kbirchard/mcphail-update/research/2015-Insect-Biometrics-Optoacoustic-Signal-McPhail-s023.TIF

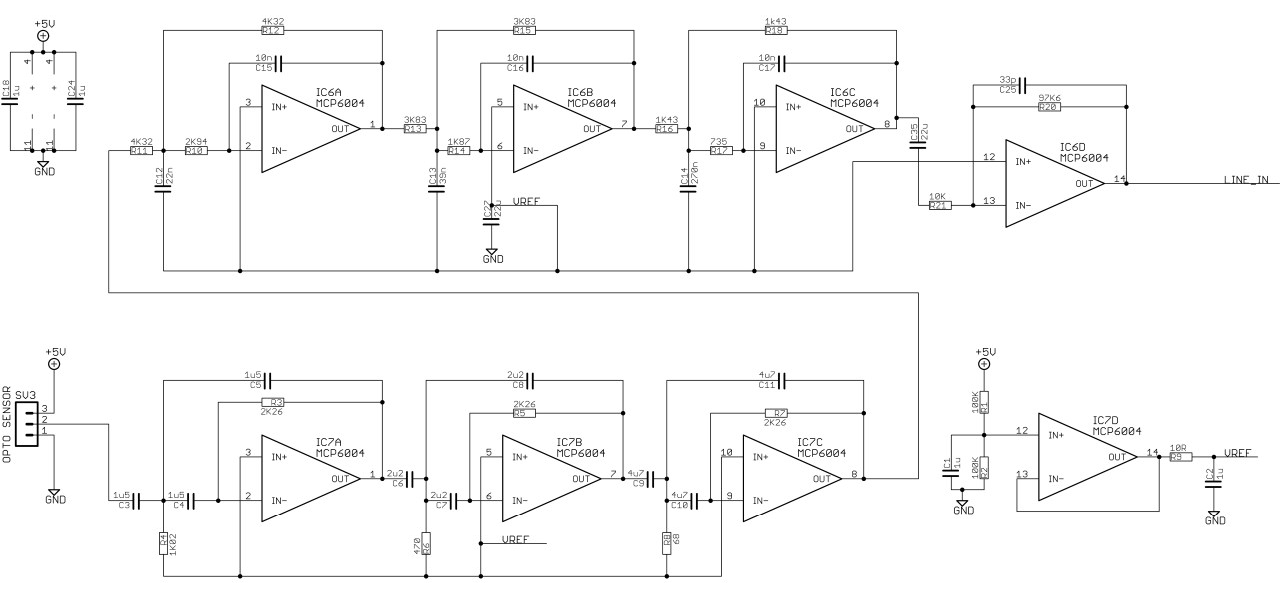
research/2015-Insect-Biometrics-Optoacoustic-Signal-McPhail-s023.TIF
