kbirchard/mcphail-update/research/2015-Insect-Biometrics-Optoacoustic-Signal-McPhail-s026.TIF

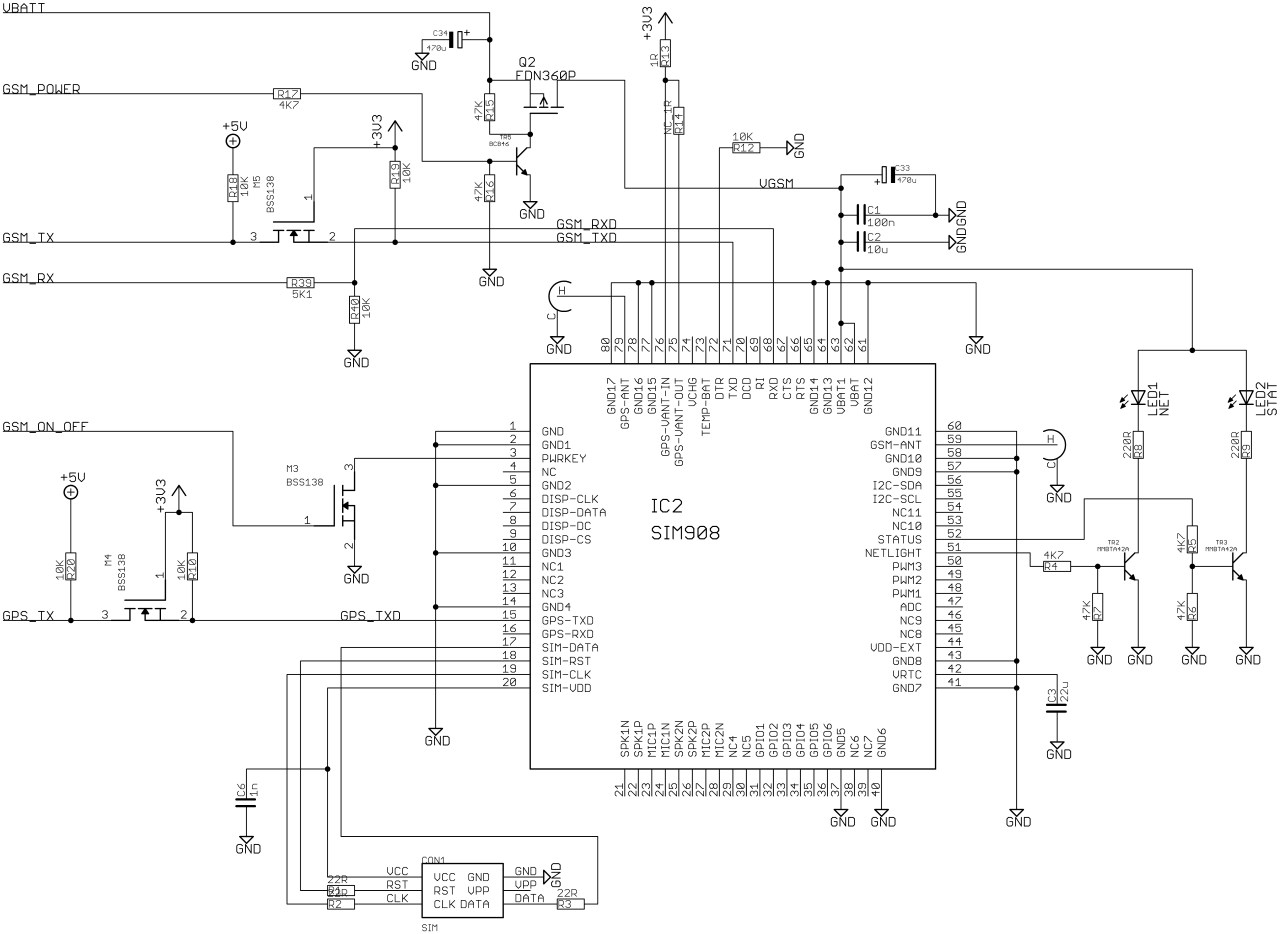
research/2015-Insect-Biometrics-Optoacoustic-Signal-McPhail-s026.TIF
