kbirchard/mcphail-update/research/2015-Insect-Biometrics-Optoacoustic-Signal-McPhail-s027.TIF

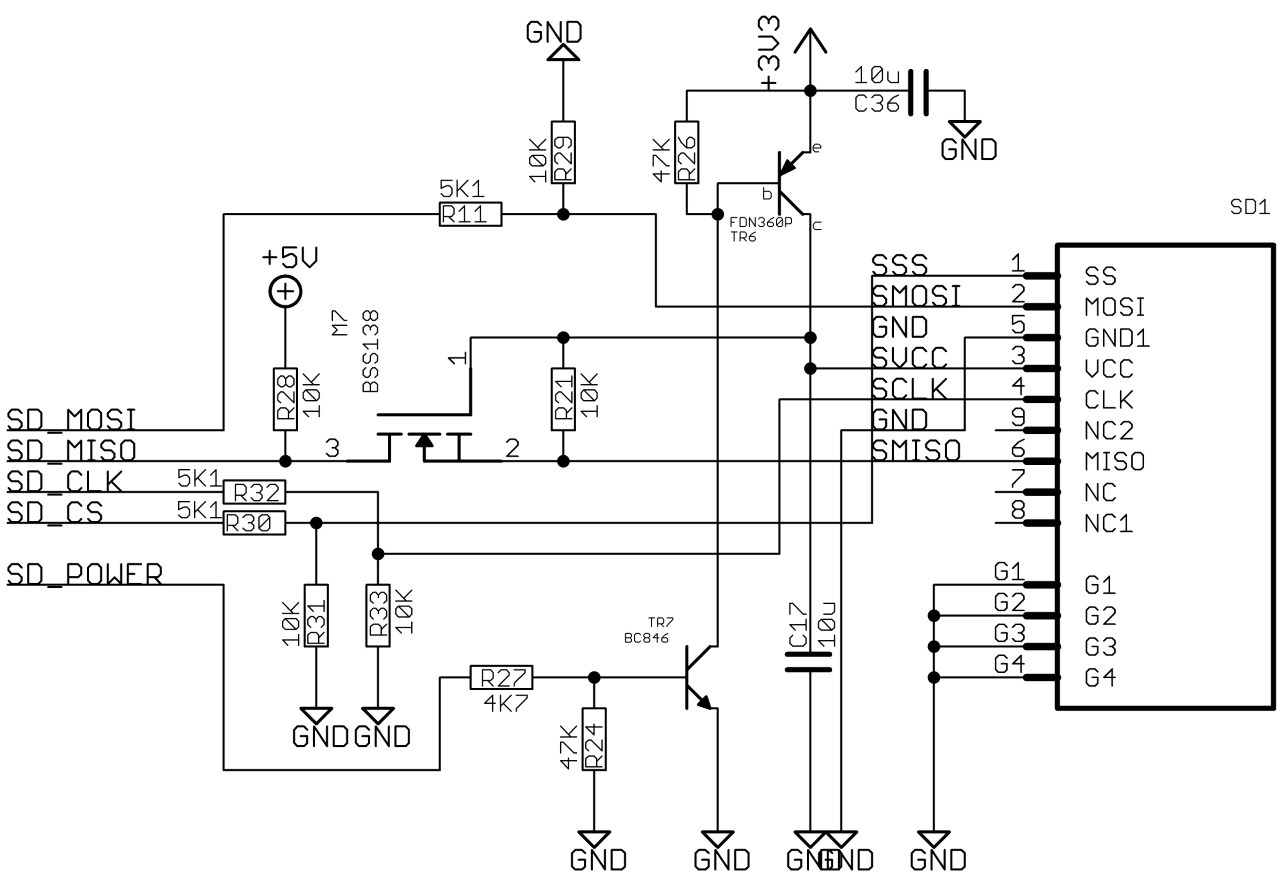
research/2015-Insect-Biometrics-Optoacoustic-Signal-McPhail-s027.TIF
