kbirchard/mcphail-update/research/signalconditioning-rearranged.png

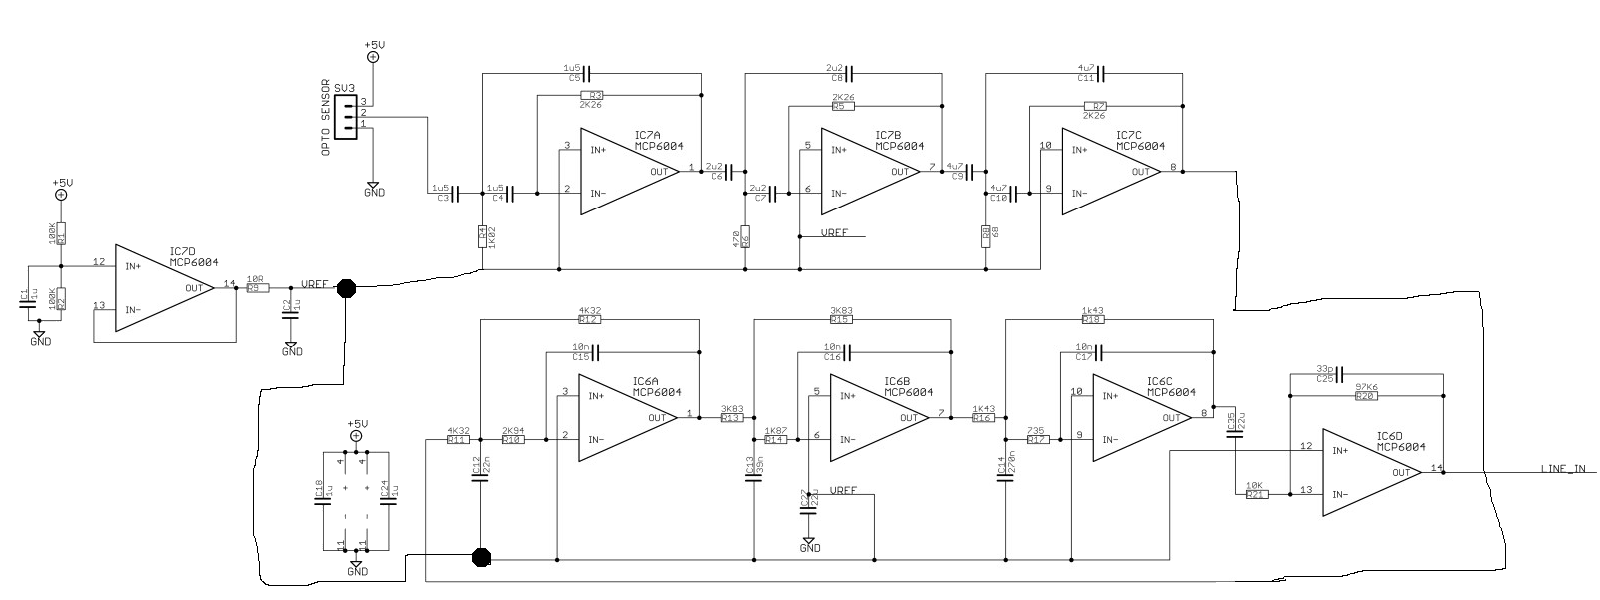
research/signalconditioning-rearranged.png
