kbirchard/mcphail-update/hardware/mcphail-ir-emitter-board/bom/mcphail-ir-emitter-board-v1.0-bom-mouser.csv

Ref | Qty | Qty3 | Description | Mouser PN
LED1 LED10 LED2 LED3 LED4 LED5 LED6 LED7 LED8 LED9 | 10 | 30 | LED IR 850NM TH SFH4356 | 720-SFH4356
