kbirchard/mcphail-update/hardware/mcphail-main-board/bom/mcphail-main-board-v1.0-bom-adafruit.csv

Ref | Qty | Qty3 | Description | Adafruit PN
B1 | 1 | 3 | Lithium Ion Polymer Battery - 3.7v 500mAh | 1578
J7 | 1 | 3 | ADAFRUIT FONA 808 + GPS | 2542
