kbirchard/mcphail-update/hardware/mcphail-ir-emitter-board/bom/mcphail-ir-emitter-board-v1.0-bom-seeed.csv

Location | MPN/Seeed SKU | Quantity
J1 | M20-9990246 | 1
LED1 LED10 LED2 LED3 LED4 LED5 LED6 LED7 LED8 LED9 | SFH 4356 | 10
