kbirchard/mcphail-update/hardware/March2018-BoardFix/20180303-McPhail_Zero_Analog_Shield_Test_Data.xlsx

Sheet: Test1
Sample # | Run Time (in microseconds) | ADC0 | ADC1 | ADC2
0 | 1557 | 724 | 521 | 523
1 | 3557 | 207 | 521 | 520
2 | 5557 | 792 | 521 | 519
3 | 7558 | 336 | 521 | 523
4 | 9558 | 473 | 522 | 516
5 | 11558 | 748 | 521 | 523
6 | 13559 | 179 | 520 | 520
7 | 15559 | 755 | 520 | 518
8 | 17559 | 345 | 521 | 523
9 | 19560 | 465 | 521 | 518
10 | 21560 | 736 | 521 | 522
11 | 23560 | 195 | 521 | 520
12 | 25561 | 785 | 521 | 519
13 | 27561 | 355 | 520 | 523
14 | 29561 | 481 | 521 | 517
15 | 31562 | 740 | 522 | 523
16 | 33562 | 185 | 521 | 520
17 | 35562 | 802 | 520 | 518
18 | 37563 | 343 | 520 | 523
19 | 39563 | 470 | 521 | 517
20 | 41563 | 748 | 520 | 522
21 | 43564 | 172 | 520 | 519
22 | 45564 | 806 | 520 | 519
23 | 47564 | 357 | 520 | 523
24 | 49565 | 472 | 520 | 516
25 | 51565 | 733 | 520 | 523
26 | 53565 | 208 | 520 | 520
27 | 55566 | 801 | 520 | 519
28 | 57566 | 363 | 521 | 523
29 | 59566 | 482 | 521 | 517
30 | 61567 | 752 | 521 | 522
31 | 63567 | 192 | 521 | 520
32 | 65567 | 818 | 520 | 519
33 | 67568 | 359 | 520 | 524
34 | 69568 | 492 | 521 | 517
35 | 71568 | 734 | 521 | 522
36 | 73569 | 195 | 520 | 519
37 | 75569 | 804 | 522 | 519
38 | 77569 | 365 | 520 | 523
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
